cnvogelg/plipbox/hardware/nano_adapter/nano_adapter.sch

## EAGLE design hardware/nano_adapter/nano_adapter.sch (2013-05-31)

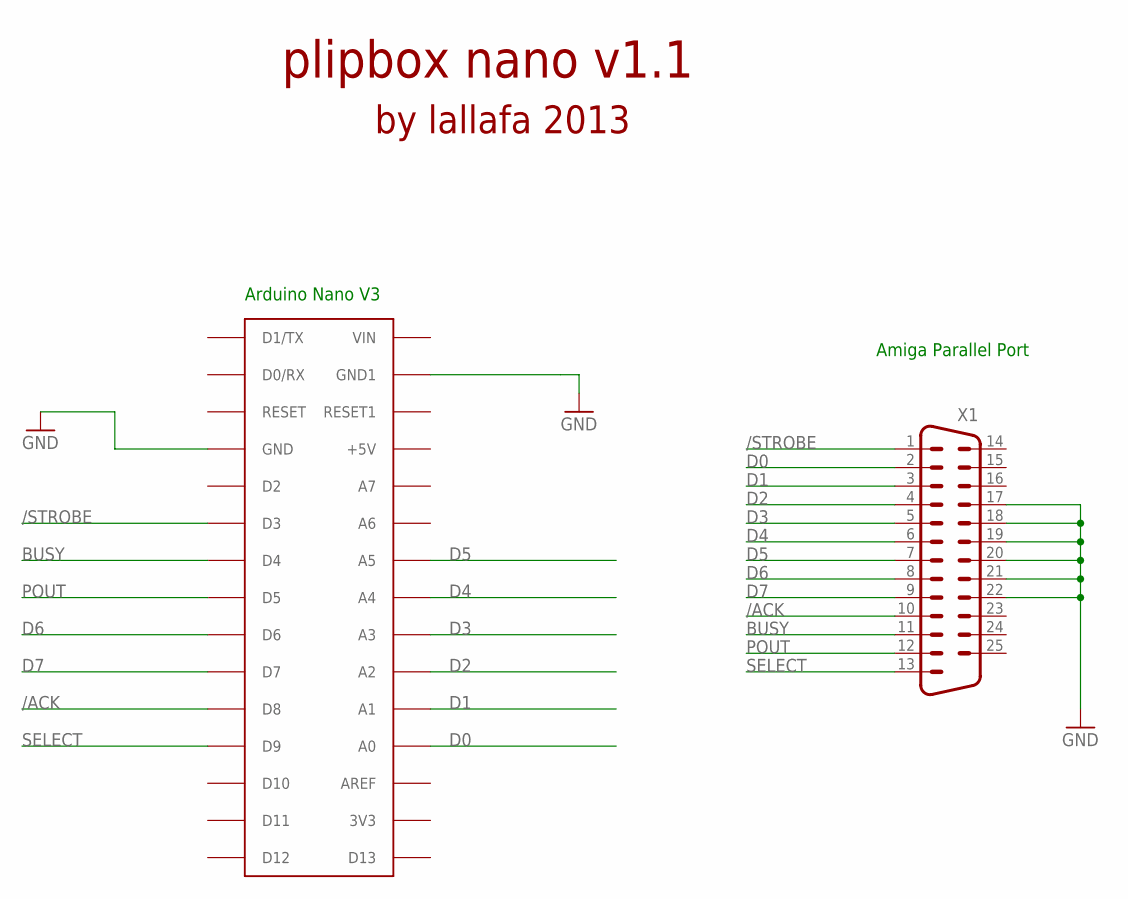
[picture p3: schematic nano_adapter.sch]

Parts:
U$1: ARDUINONANO; PDIP-32
X1: M25HP

Connections:
/ACK: U$1.D8, X1.10
/STROBE: U$1.D3, X1.1
BUSY: U$1.D4, X1.11
D0: U$1.A7 (A0), X1.2
D1: U$1.A6 (A1), X1.3
D2: U$1.A5 (A2), X1.4
D3: U$1.A4 (A3), X1.5
D4: U$1.A3 (A4), X1.6
D5: U$1.A2 (A5), X1.7
D6: U$1.D6, X1.8
D7: U$1.D7, X1.9
GND: U$1.GND, U$1.GND1, X1.17, X1.18, X1.19, X1.20, X1.21, X1.22
POUT: U$1.D5, X1.12
SELECT: U$1.D9, X1.13

Notes on the sheet:
Arduino Nano V3
Amiga Parallel Port
plipbox nano v1.1
by lallafa 2013
