cnvogelg/plipbox/avr/src/dump.c

/*
 * dump.c - helper functions for debugging
 *
 * Written by
 *  Christian Vogelgsang <chris@vogelgsang.org>
 *
 * This file is part of pbprotobox.
 * See README for copyright notice.
 *
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
 */

#include "dump.h"
#include "uart.h"
#include "uartutil.h"
#include "net/net.h"
#include "net/arp.h"
#include "net/eth.h"
#include "net/ip.h"
#include "net/udp.h"
#include "net/tcp.h"
#include "param.h"
#include "util.h"
#include "pb_proto.h"

void dump_eth_pkt(const u08 *eth_buf, u16 size)
{
  u08 buf[4];
  
  uart_send('[');
  dword_to_dec(size, buf, 4, 4);
  uart_send_data(buf,4);
  uart_send(',');
  uart_send_hex_word(eth_get_pkt_type(eth_buf));
  uart_send(',');
  net_dump_mac(eth_get_src_mac(eth_buf));
  uart_send('>');
  net_dump_mac(eth_get_tgt_mac(eth_buf));
  uart_send(']');
  uart_send(' ');
}

void dump_arp_pkt(const u08 *arp_buf)
{
  uart_send_pstring(PSTR("[ARP:"));

  // ARP op
  u16 op = arp_get_op(arp_buf);
  if(op == ARP_REQUEST) {
    uart_send_pstring(PSTR("REQ "));
  } else if(op == ARP_REPLY) {
    uart_send_pstring(PSTR("REPL"));
  } else {
    uart_send_hex_word(op);
  }
  uart_send(',');
  
  // src pair
  uart_send('(');
  net_dump_mac(arp_get_src_mac(arp_buf));
  uart_send(',');
  net_dump_ip(arp_get_src_ip(arp_buf));
  uart_send(')');
  uart_send('>');

  // tgt pair
  uart_send('(');
  net_dump_mac(arp_get_tgt_mac(arp_buf));
  uart_send(',');
  net_dump_ip(arp_get_tgt_ip(arp_buf));
  uart_send(')');
  
  uart_send(']');
  uart_send(' ');
}

void dump_ip_pkt(const u08 *ip_buf)
{
  uart_send_pstring(PSTR("[IP4:"));

  // size
  uart_send_hex_word(ip_get_total_length(ip_buf));

  // ip proto
  u08 proto = ip_get_protocol(ip_buf);
  if(proto == IP_PROTOCOL_ICMP) {
    uart_send_pstring(PSTR(",ICMP"));
  } else if(proto == IP_PROTOCOL_TCP) {
    uart_send_pstring(PSTR(",TCP "));
  } else if(proto == IP_PROTOCOL_UDP) {
    uart_send_pstring(PSTR(",UDP "));
  } else {
    uart_send(',');
    uart_send_hex_word(proto);
  }

  // src/tgt ip
  uart_send(',');
  net_dump_ip(ip_get_src_ip(ip_buf));
  uart_send('>');
  net_dump_ip(ip_get_tgt_ip(ip_buf)),

  uart_send(']');
  uart_send(' ');
}

static void dump_udp_port(u16 port)
{
  if(port == 67) {
    uart_send_pstring(PSTR("BOOTPS"));
  } else if(port == 68) {
    uart_send_pstring(PSTR("BOOTPC"));
  } else {
    uart_send(' ');
    uart_send_hex_word(port);
    uart_send(' ');
  }
}

static void dump_tcp_port(u16 port)
{
  if(port == 21) {
    uart_send_pstring(PSTR("FTPctl"));
  } else if(port == 20) {
    uart_send_pstring(PSTR("FTPdat"));
  } else {
    uart_send(' ');
    uart_send_hex_word(port);
    uart_send(' ');
  }
}

extern void dump_ip_protocol(const u08 *ip_buf)
{
  const u08 *proto_buf = ip_buf + ip_get_hdr_length(ip_buf);
  u08 proto = ip_get_protocol(ip_buf);
  if(proto == IP_PROTOCOL_UDP) {
    uart_send_pstring(PSTR("[UDP:"));
    u16 src_port = udp_get_src_port(proto_buf);
    u16 tgt_port = udp_get_tgt_port(proto_buf);
    dump_udp_port(src_port);
    uart_send('>');
    dump_udp_port(tgt_port);
    uart_send(']');
    uart_send(' ');
  }
  else if(proto == IP_PROTOCOL_TCP) {
    uart_send_pstring(PSTR("[TCP:"));
    u16 src_port = tcp_get_src_port(proto_buf);
    u16 tgt_port = tcp_get_tgt_port(proto_buf);
    dump_tcp_port(src_port);
    uart_send('>');
    dump_tcp_port(tgt_port);

    u16 flags = tcp_get_flags(proto_buf);
    uart_send_pstring(PSTR(",flags="));
    uart_send_hex_word(flags);

    uart_send_pstring(PSTR(",seq="));
    u32 seq = tcp_get_seq_num(proto_buf);
    uart_send_hex_dword(seq);
    
    if(flags & TCP_FLAGS_ACK) {
      u32 ack = tcp_get_ack_num(proto_buf);
      uart_send_pstring(PSTR(",ack="));
      uart_send_hex_dword(ack);
    }
    
    uart_send(']');
    uart_send(' ');
  }
}

extern void dump_line(const u08 *eth_buf, u16 size)
{
  dump_eth_pkt(eth_buf, size);
  
  const u08 *ip_buf = eth_buf + ETH_HDR_SIZE;
  u16 type = eth_get_pkt_type(eth_buf);
  if(type == ETH_TYPE_ARP) {
    dump_arp_pkt(ip_buf);
  } else if(type == ETH_TYPE_IPV4) {
    dump_ip_pkt(ip_buf);
    dump_ip_protocol(ip_buf);
  }
}

void dump_pb_cmd(const pb_proto_stat_t *ps)
{
  u08 buf[4];
  
  uart_send_time_stamp_spc();

  // show command
  u08 cmd = ps->cmd;
  u08 is_valid = 1;
  switch(cmd) {
    case PBPROTO_CMD_SEND:
    case PBPROTO_CMD_SEND_BURST:
      break;
    case PBPROTO_CMD_RECV:
    case PBPROTO_CMD_RECV_BURST:
      break;
    default:
      is_valid = 0;
      break;
  }

  u08 status = ps->status;

  // invalid command
  if(!is_valid) {
    uart_send_pstring(PSTR("cmd="));
    uart_send_hex_byte(cmd);
    uart_send_pstring(PSTR("?? ERR:"));
    uart_send_hex_byte(status);
    uart_send_crlf();
    return;
  }

  PGM_P str = ps->is_send ? PSTR("[TX:") : PSTR("[RX:");
  uart_send_pstring(str);
  uart_send_hex_byte(cmd);

  // result
  if(status == PBPROTO_STATUS_OK) {
    uart_send_pstring(PSTR("] ok"));
  } else {
    uart_send_pstring(PSTR("] ERR:"));
    uart_send_hex_byte(status);
  }

  // packet size
  uart_send_pstring(PSTR(" n="));
  dword_to_dec(ps->size, buf, 4, 4);
  uart_send_data(buf,4);

  // packet delta
  uart_send_pstring(PSTR(" d="));
  dword_to_dec(ps->delta, buf, 4, 4);  
  uart_send_data(buf,4);

  // speed
  uart_send_pstring(PSTR(" v="));
  uart_send_rate_kbs(ps->rate);

  // request delay
  if(!ps->is_send) {
    uart_send_pstring(PSTR("  +req="));
    uart_send_delta(ps->recv_delta);
  }
  uart_send_crlf();
}
