cnvogelg/plipbox/avr/src/pb_io.c

/*
 * pb_io.c: handle incoming plipbox packets
 *
 * Written by
 *  Christian Vogelgsang <chris@vogelgsang.org>
 *
 * This file is part of plipbox.
 * See README for copyright notice.
 *
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
 */

#include "global.h"
   
#include "net/net.h"
#include "net/eth.h"
#include "net/ip.h"
#include "net/arp.h"

#include "pkt_buf.h"
#include "pktio.h"
#include "pb_proto.h"
#include "uart.h"
#include "uartutil.h"
#include "param.h"
#include "dump.h"
#include "timer.h"
#include "stats.h"
#include "eth_state.h"
#include "util.h"
#include "pb_io.h"

static u16 offset;
static u16 size;
static u08 send_magic;

// SANA driver parameters sent in magic packet
u08 sana_online;
u08 sana_mac[6];
u08 sana_version[2];

// ----- send callbacks -----

static void rx_begin(u16 *pkt_size)
{
  // start writing packet with eth header
  offset = 0;
  pktio_tx_begin(*pkt_size);
  size = *pkt_size;
}

static void rx_data(u08 *data)
{
  // clone packet to our packet buffer
  if(offset < PKT_BUF_SIZE) {
    rx_pkt_buf[offset] = *data;
  }
  
  if(offset < size) {
    // always copy to TX buffer of pktio
    pktio_tx_byte(*data);
  }

  offset ++;
}

static void rx_end(u16 pkt_size)
{
  // end range in pktio buffer
  pktio_tx_end();
  rx_pkt_size = pkt_size;
}

// ----- recv callbacks -----

static void tx_begin(u16 *pkt_size)
{
  // report size of packet
  *pkt_size = tx_pkt_size;
  offset = 0;
  size = tx_pkt_size;

  if(!send_magic) {
    pktio_rx_data_begin();
  }
}

static void tx_data(u08 *data)
{
  // clone packet to our packet buffer
  if(offset < PKT_BUF_SIZE) {
    *data = tx_pkt_buf[offset];
  } else if(offset < size) {
    *data = pktio_rx_byte();    
  } else {
    *data = 0;
  }
  offset ++;
}

static void tx_end(u16 pkt_size)
{
  // reset size of packet
  tx_pkt_size = 0;

  if(send_magic) {
    send_magic = 0;
  } else {
    pktio_rx_data_end();
    pktio_rx_end();
  }
}

// ----- function table -----

static pb_proto_funcs_t funcs = {
  .send_begin = rx_begin,
  .send_data = rx_data,
  .send_end = rx_end,
  
  .recv_begin = tx_begin,
  .recv_data = tx_data,
  .recv_end = tx_end
};

// ----- functions -----

void pb_io_init(void)
{
  pb_proto_init(&funcs);
}

static void uart_send_prefix_pbp(void)
{
  uart_send_time_stamp_spc();
  uart_send_pstring(PSTR("pbp(rx): "));
}

static void uart_send_prefix_eth(void)
{
  uart_send_time_stamp_spc();
  uart_send_pstring(PSTR("eth(TX): "));
}

//#define DEBUG

static u08 filter_arp_pkt(void)
{
  u08 *arp_buf = rx_pkt_buf + ETH_HDR_SIZE;
  u16 arp_size = rx_pkt_size;
  
  // make sure its an IPv4 ARP packet
  if(!arp_is_ipv4(arp_buf, arp_size)) {
    uart_send_prefix_pbp();
    uart_send_pstring(PSTR("ARP: type?"));
    uart_send_crlf();
    return 0;
  }

  // ARP request should now be something like this:
  // src_mac = Amiga MAC
  // src_ip = Amiga IP
  const u08 *pkt_src_mac = eth_get_src_mac(rx_pkt_buf);
  const u08 *arp_src_mac = arp_get_src_mac(arp_buf);
  
  // pkt src and arp src must be the same
  if(!net_compare_mac(pkt_src_mac, arp_src_mac) && !net_compare_zero_mac(pkt_src_mac)) {
    uart_send_prefix_pbp();
    uart_send_pstring(PSTR("ARP: pkt!=src mac!"));
    uart_send_crlf();
    return 0;
  }
  return 1;
}

static void send(void)
{
  // dump eth packet
  if(param.dump_dirs & DUMP_DIR_ETH_TX) {
    uart_send_prefix_eth();
    dump_line(rx_pkt_buf, rx_pkt_size);
    uart_send_crlf();
  }

  // finally send ethernet packet
  pktio_tx_send(rx_pkt_size);
}

static void handle_magic_online(void)
{
  net_copy_mac(eth_get_src_mac(rx_pkt_buf), sana_mac);
  const u08 *ver = eth_get_tgt_mac(rx_pkt_buf);
  sana_version[0] = ver[0];
  sana_version[1] = ver[1];
  
  // always show online state
  uart_send_prefix_pbp();
  uart_send_pstring(PSTR("online: mac="));
  net_dump_mac(sana_mac);
  uart_send_pstring(PSTR(" ver="));
  uart_send_hex_byte(sana_version[0]);
  uart_send('.');
  uart_send_hex_byte(sana_version[1]);
  uart_send_crlf();
  
  /* neet to reconfigure eth? */
  if(!net_compare_mac(sana_mac, param.mac_addr)) {
    net_copy_mac(sana_mac, param.mac_addr);
    param_save(); /* save changed mac to eeprom */
    eth_state_configure(); /* configure eth to set new mac */
  }

  /* does versions match? */
  if((sana_version[0] == VERSION_MAJ) && (sana_version[1] == VERSION_MIN)) {  
    sana_online = 1;
  } else {
    uart_send_pstring(PSTR("VERSION MISMATCH! please update firmware."));
    uart_send_crlf();
    sana_online = 0;
  }
}

static void handle_magic_offline(void)
{
  uart_send_prefix_pbp();
  uart_send_pstring(PSTR("offline"));
  uart_send_crlf();
  
  sana_online = 0;
}

#define MAGIC_ONLINE 0xffff
#define MAGIC_OFFLINE 0xfffe

// packet arrived from Amiga. now sent via Ethernet
static void handle_pb_send(u08 eth_online)
{
  u08 dump_it = param.dump_dirs & DUMP_DIR_PLIP_RX;  
  
  // got a valid packet from plip -> check type
  u16 type = eth_get_pkt_type(rx_pkt_buf);

  // dump packet?
  if(dump_it) {
    uart_send_prefix_pbp();
    dump_line(rx_pkt_buf, rx_pkt_size);
    uart_send_crlf();
  }

  // flag if packet will be sent via ethernet
  u08 send_it = 0;
  
  // ----- magic packets from SANA driver? -----
  // magic online packet?
  if(type == MAGIC_ONLINE) {
    handle_magic_online();
  }
  // magic offline packet?
  else if(type == MAGIC_OFFLINE) {
    handle_magic_offline();
  }
  else {
    // ----- packet filtering? -----
    if(param.filter_plip) {
      if(type == ETH_TYPE_IPV4) {
        send_it = 1;
      }
      // handle ARP packet
      else if(type == ETH_TYPE_ARP) {
        send_it = filter_arp_pkt();
      }
      // unknown packet type
      else {
        uart_send_prefix_pbp();
        uart_send_pstring(PSTR("type? "));
        uart_send_hex_word(type);
        uart_send_crlf();
        send_it = 0;
      }
    } else {
      send_it = 1;
    }
  }
  
  // send to ethernet
  if(send_it) {
    if(eth_online) {
      stats.tx_cnt ++;
      stats.tx_bytes += rx_pkt_size;    
      send();
    } else {
      // no ethernet online -> we have to drop packet
      uart_send_prefix_eth();
      uart_send_pstring(PSTR("Offline -> DROP!"));
      uart_send_crlf();
      stats.tx_drop ++;
      pktio_tx_reject();
    }      
  } else {
    stats.tx_filter ++;
    pktio_tx_reject();
  }    
}

void pb_io_send_magic(u16 type, u08 extra_size)
{
  // set tx packet size so no ethernet frames are written in packet buffer
  tx_pkt_size = 14 + extra_size;
  send_magic = 1;

  // fill ethernet header
  u08 *ptr = tx_pkt_buf;
  net_copy_bcast_mac(ptr);
  ptr += 6;
  net_copy_mac(param.mac_addr, ptr);
  ptr += 6;
  net_put_word(ptr, type);

  // now request receive from Amiga
  pb_proto_request_recv();

  // report
  uart_send_prefix_pbp();
  uart_send_pstring(PSTR("send magic "));
  uart_send_hex_word(type);
  uart_send_crlf();
}

extern u32 req_time;

u08 pb_io_worker(u08 plip_state, u08 eth_online)
{
  // call protocol handler (low level transmit)
  u08 cmd;
  u16 size;
  u32 start = time_stamp;
  u08 status = pb_proto_handle(&cmd, &size);
  u32 end = time_stamp;
  
  // nothing done... return
  if(status == PBPROTO_STATUS_IDLE) {
    return PB_IO_IDLE; // was passive
  }
  else if(status == PBPROTO_STATUS_OK) {
    u32 delta = end - start;

    // dump ok command if requested
    if(param.dump_plip) {
      dump_pb_cmd(cmd, status, size, delta, start - req_time);
    }
    
    // do we have a packet received?
    if((cmd == PBPROTO_CMD_SEND) || (cmd == PBPROTO_CMD_SEND_BURST)) {
      handle_pb_send(eth_online);
    }

    // update rate
    u16 rate = calc_rate_kbs(size, delta);
    if(cmd == PBPROTO_CMD_SEND) {
      if(rate > stats.tx_max_rate) {
        stats.tx_max_rate = rate;
      }
    } else {
      if(rate > stats.rx_max_rate) {
        stats.rx_max_rate = rate;
      }
    }
    return PB_IO_OK;
  }
  else {
    u32 delta = end - start;
    u32 latency = start - req_time;
    
    // dump error
    dump_pb_cmd(cmd, status, size, delta, latency);

    return PB_IO_ERROR;
  }
}
