cnvogelg/plipbox/src/eth_tx.c

/*
 * eth_tx.c: handle eth packet sends
 *
 * Written by
 *  Christian Vogelgsang <chris@vogelgsang.org>
 *
 * This file is part of plip2slip.
 * See README for copyright notice.
 *
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
 */

#include "global.h"
   
#include "net.h"
#include "eth.h"
#include "ip.h"
#include "arp.h"
#include "icmp.h"
#include "pkt_buf.h"
#include "enc28j60.h"

#include "plip.h"

#include "uart.h"
#include "uartutil.h"
   
#define DEBUG_ETH_TX   

u08 eth_tx_send_ping_request(const u08 *ip)
{
#ifdef DEBUG_ETH_TX
  uart_send_string("send ping: ");
  net_dump_ip(ip);
#endif

  const u08 *mac = arp_find_mac(pkt_buf, ip);
  if(mac == 0) {
#ifdef DEBUG_ETH_TX
    uart_send_string("no mac!");
    uart_send_crlf();
#endif
    return 0;
  }
  
#ifdef DEBUG_ETH_TX
  uart_send_string(" -> ");
  net_dump_mac(mac);
  uart_send_crlf();
#endif
  
  eth_make_to_tgt(pkt_buf, ETH_TYPE_IPV4, mac);
  u08 *ip_pkt = pkt_buf + ETH_HDR_SIZE;
  u16 size = icmp_make_ping_request(ip_pkt, ip, 0, 0);
  enc28j60_packet_tx(pkt_buf, size + ETH_HDR_SIZE);
  
  return 1;
}

static void handle_my_packet(u08 *ip_buf, u16 size)
{
  // TODO
}

static u08 offset;

static u08 begin_rx(plip_packet_t *pkt)
{
  // start writing packet after (potential) ETH header
  offset = ETH_HDR_SIZE;
  
  // start writing after ETH header
  enc28j60_packet_tx_begin_range(ETH_HDR_SIZE);
  
  return PLIP_STATUS_OK;
}

static u08 transfer_rx(u08 *data)
{
  // clone packet to our packet buffer
  if(offset < PKT_BUF_SIZE) {
    pkt_buf[offset] = *data;
    offset ++;
  }
  
  // always copy to TX buffer of enc28j60
  enc28j60_packet_tx_byte(*data);
  
  return PLIP_STATUS_OK;
}

static u08 end_rx(plip_packet_t *pkt)
{
  // end range in enc28j60 buffer
  enc28j60_packet_tx_end_range();

  return PLIP_STATUS_OK;
}

void eth_tx_init(void)
{
  plip_recv_init(begin_rx, transfer_rx, end_rx);
}

void eth_tx_worker(void)
{
  // do we have a PLIP packet waiting?
  if(plip_can_recv() == PLIP_STATUS_OK) {
    
    // prepare eth chip to get its tx buffer filled
    enc28j60_packet_tx_prepare();
    
    // receive PLIP packet and store it in eth chip tx buffer
    // also keep a copy in our local pkt_buf (up to max size)
    u08 status = plip_recv(&pkt);
    
    // if PLIP rx was ok then have a look at the packet
    if(status != PLIP_STATUS_OK) {
      uart_send_string("plip_rx:");
      uart_send_hex_byte_crlf(status);
    } else {
      // fetch tgt ip of incoming packet
      u08 *ip_buf = pkt_buf + ETH_HDR_SIZE;
      const u08 *tgt_ip = ip_get_tgt_ip(ip_buf);
      u08 ltgt_ip[4];
      net_copy_ip(tgt_ip, ltgt_ip);
      const u08 *src_ip = ip_get_src_ip(ip_buf);
  
      // make sure all packets are coming from amiga
      if(!net_compare_ip(src_ip, net_get_p2p_amiga())) {
        uart_send_string("plip_rx: not amiga!");
        uart_send_crlf();
        return;
      }
  
      // if its a packet for me (p2p or eth address) then handle it now
      if(net_compare_ip(ltgt_ip, net_get_p2p_me()) ||
         net_compare_ip(ltgt_ip, net_get_ip())) {
        uart_send_string("plip_rx: ME!");
        uart_send_crlf();
        handle_my_packet(ip_buf, pkt.size);
      } 
      // pass this packet on to ethernet
      else {
#ifdef DEBUG
        uart_send_string("plip_rx:");
        net_dump_ip(ltgt_ip);
        uart_send_string(" size=");
        uart_send_hex_word_spc(pkt.size);
#endif
        
        // find a mac address for the target 
        const u08 *mac = arp_find_mac(pkt_buf, ltgt_ip);
        if(mac == 0) {
          uart_send_string("??");
          uart_send_crlf();
        }
        // found mac -> we can send packet
        else {
#ifdef DEBUG
          uart_send_string(" -> mac ");
          net_dump_mac(mac);
          uart_send_crlf();
#endif
        
          // ----- NAT -----
          // adjust source ip to our eth IP
          ip_adjust_checksum(ip_buf, IP_CHECKSUM_OFF, net_get_p2p_amiga(), net_get_ip());
          
          // get protocol
          u08 protocol = ip_get_protocol(ip_buf);
          u16 copy_size = ETH_HDR_SIZE + IP_MIN_HDR_SIZE;
          if(protocol == IP_PROTOCOL_TCP) {
            // adjust TCP checksum
            u16 off = ip_get_hdr_length(ip_buf) + TCP_CHECKSUM_OFF;
            ip_adjust_checksum(ip_buf, off, net_get_p2p_amiga(), net_get_ip());
            copy_size += TCP_CHECKSUM_OFF + 2;
          } else if(protocol == IP_PROTOCOL_UDP) {
            // adjust UDP checksum
            u16 off = ip_get_hdr_length(ip_buf) + UDP_CHECKSUM_OFF;
            ip_adjust_checksum(ip_buf, off, net_get_p2p_amiga(), net_get_ip());
            copy_size += UDP_CHECKSUM_OFF + 2;
          }

          // change src ip to my eth ip
          ip_set_src_ip(ip_buf, net_get_ip());
          
#ifdef DEBUG
          // make sure our checksum was corrected correctly
          u16 chk = ip_hdr_calc_checksum(ip_buf);
          if(chk != 0xffff) {
            uart_send_string("eth_tx:CHECK?");
            uart_send_hex_word_crlf(chk);
          }
#endif
        
          // now build ethernet header
          eth_make_to_tgt(pkt_buf, ETH_TYPE_IPV4, mac);
        
          // copy (created) eth header and (modified) ip header back to packet buffer
          enc28j60_packet_tx_begin_range(0);
          enc28j60_packet_tx_blk(pkt_buf, copy_size);
          enc28j60_packet_tx_end_range();
  
          // finally send packet
          u16 pkt_size = pkt.size + ETH_HDR_SIZE;
          enc28j60_packet_tx_send(pkt_size);
        }
      }
    }
  }
}
