cnvogelg/plipbox/avr/src/param.c

/*
 * param.c - handle device parameters
 *
 * Written by
 *  Christian Vogelgsang <chris@vogelgsang.org>
 *
 * This file is part of plipbox.
 * See README for copyright notice.
 *
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
 */

#include "param.h"
#include "uartutil.h"
#include "uart.h"
#include "net/net.h"

#include <avr/eeprom.h>
#include <util/crc16.h>
#include <avr/pgmspace.h>
#include <string.h>

// current memory RAM param
param_t param;

// eeprom param
param_t eeprom_param EEMEM;
uint16_t eeprom_crc16 EEMEM;

// default 
static const param_t PROGMEM default_param = {
  .mac_addr = { 0x1a,0x11,0xaf,0xa0,0x47,0x11},

  .flow_ctl = 0,
  .full_duplex = 0,
  
  .test_plen = 1514,
  .test_ptype = 0xfffd,
  .test_ip = { 192,168,2,222 },
  .test_port = 6800,
  .test_mode = 0
};

static void dump_byte(PGM_P str, const u08 val)
{
  uart_send_pstring(str);
  uart_send_hex_byte(val);
  uart_send_crlf();  
}

static void dump_word(PGM_P str, const u16 val)
{
  uart_send_pstring(str);
  uart_send_hex_word(val);
  uart_send_crlf();    
}

// dump all params
void param_dump(void)
{
  // mac address
  uart_send_pstring(PSTR("m: mac address   "));
  net_dump_mac(param.mac_addr);
  uart_send_crlf();

  // options
  uart_send_crlf();
  dump_byte(PSTR("fd: full duplex  "), param.full_duplex);
  dump_byte(PSTR("fc: flow control "), param.flow_ctl);
  
  // test
  uart_send_crlf();
  dump_word(PSTR("tl: packet len   "), param.test_plen);
  dump_word(PSTR("tt: packet type  "), param.test_ptype);
  uart_send_pstring(PSTR("ti: ip address   "));
  net_dump_ip(param.test_ip);
  uart_send_crlf();
  dump_word(PSTR("tp: udp port     "), param.test_port);
  dump_byte(PSTR("tm: test mode    "), param.test_mode);
}

// build check sum for parameter block
static uint16_t calc_crc16(param_t *p)
{
  uint16_t crc16 = 0xffff;
  u08 *data = (u08 *)p;
  for(u16 i=0;i<sizeof(param_t);i++) {
    crc16 = _crc16_update(crc16,*data);
    data++;
  }
  return crc16;
}

u08 param_save(void)
{
  // check that eeprom is writable
  if(!eeprom_is_ready())
    return PARAM_EEPROM_NOT_READY;

  // write current param to eeprom
  eeprom_write_block(&param,&eeprom_param,sizeof(param_t));

  // calc current parameter crc
  uint16_t crc16 = calc_crc16(&param);
  eeprom_write_word(&eeprom_crc16,crc16);

  return PARAM_OK;
}

u08 param_load(void)
{
  // check that eeprom is readable
  if(!eeprom_is_ready())
    return PARAM_EEPROM_NOT_READY;
  
  // read param
  eeprom_read_block(&param,&eeprom_param,sizeof(param_t));
  
  // read crc16
  uint16_t crc16 = eeprom_read_word(&eeprom_crc16);
  uint16_t my_crc16 = calc_crc16(&param);
  if(crc16 != my_crc16) {
    param_reset();
    return PARAM_EEPROM_CRC_MISMATCH;
  }
  
  return PARAM_OK;
}

void param_reset(void)
{
  // restore default param
  u08 *out = (u08 *)&param;
  const u08 *in = (const u08 *)&default_param;
  for(u08 i=0;i<sizeof(param_t);i++) {
    *(out++) = pgm_read_byte_near(in++);
  }
}

void param_init(void)
{
  if(param_load()!=PARAM_OK)
    param_reset();
}
