cnvogelg/plipbox/avr/src/pb_proto.h

/*
 * pb_proto.h - avr implementation of the plipbox protocol
 *
 * Written by
 *  Christian Vogelgsang <chris@vogelgsang.org>
 *
 * This file is part of plipbox.
 * See README for copyright notice.
 *
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
 */

#ifndef PBPROTO_H
#define PBPROTO_H

#include "global.h"

// status return
#define PBPROTO_STATUS_IDLE              0
#define PBPROTO_STATUS_OK                1
#define PBPROTO_STATUS_TIMEOUT           2
#define PBPROTO_STATUS_LOST_SELECT       3
#define PBPROTO_STATUS_INVALID_CMD       4
#define PBPROTO_STATUS_PACKET_TOO_LARGE  5
#define PBPROTO_STATUS_ERROR             6

// protocol stages for error reprots
#define PBPROTO_STAGE_END_SELECT         0x10
#define PBPROTO_STAGE_SIZE_HI            0x20
#define PBPROTO_STAGE_SIZE_LO            0x30
#define PBPROTO_STAGE_DATA               0x40
#define PBPROTO_STAGE_LAST_DATA          0x50
#define PBPROTO_STAGE_BURST_LO           0x60
#define PBPROTO_STAGE_BURST_HI           0x70
#define PBPROTO_STAGE_INPUT              0x80

// commands
#define PBPROTO_CMD_SEND       0x11   // amiga wants to send a packet
#define PBPROTO_CMD_RECV       0x22   // amiga wants to receive a packet
#define PBPROTO_CMD_SEND_BURST 0x33
#define PBPROTO_CMD_RECV_BURST 0x44

// line status
#define PBPROTO_LINE_OFF       0x0
#define PBPROTO_LINE_DISABLED  0x7
#define PBPROTO_LINE_OK        0x1

// callbacks
typedef u08 (*pb_proto_fill_func)(u08 *buf,u16 max_size,u16 *size);
typedef u08 (*pb_proto_proc_func)(const u08 *buf, u16 size);

typedef struct {
  u08 cmd;		// received pb proto command
  u08 status;   // status after processing the command
  u08 is_send;    // was a transmit command (amiga send?)
  u08 stats_id; // what id to use for stats recording
  u16 size;     // packet size 
  u16 delta;    // hw timing for transmit
  u16 rate;     // delta converted to transfer rate
  u16 recv_delta; // delta after recv was requested 
  u32 ts;       // time stamp of transfer
} pb_proto_stat_t;

extern pb_proto_stat_t pb_proto_stat; // filled by pb_proto_handle()

// ----- Parameter -----

extern u16 pb_proto_rx_timeout; // timeout for next byte in 100us

// ----- API -----

extern void pb_proto_init(pb_proto_fill_func fill_func, pb_proto_proc_func proc_func, u08 *buf, u16 buf_size);
extern u08  pb_proto_get_line_status(void);
extern u08  pb_proto_handle(void); // side effect: fill pb_proto_stat!
extern void pb_proto_request_recv(void);

#endif
