cnvogelg/plipbox/avr/src/pio.c

/*
 * pio.c - generic interface for packet I/O
 *
 * Written by
 *  Christian Vogelgsang <chris@vogelgsang.org>
 *
 * This file is part of plipbox.
 * See README for copyright notice.
 *
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
 */

#include "pio.h"
#include "pio_dev.h"
#include "uartutil.h"
#include "net/net.h"

#ifdef DEV_ENC28J60
#include "enc28j60.h"
#endif

// the table of available devices
static const pio_dev_ptr_t PROGMEM devices[] = {
#ifdef DEV_ENC28J60
  &pio_dev_enc28j60,
#endif
};
#define NUM_DEVICES  (sizeof(devices) / sizeof(pio_dev_ptr_t))

// index of active device
static u08 dev_id;
static pio_dev_ptr_t cur_dev;

u08 pio_set_device(u08 id)
{
  if(id < NUM_DEVICES) {
    dev_id = id;
    return 1;
  }
  // invalid device selected
  return 0;
}

u08 pio_init(const u08 mac[6],u08 flags)
{
  // get current device
  cur_dev = (pio_dev_ptr_t)pgm_read_word(devices + dev_id);

  // show hello
  uart_send_time_stamp_spc();
  uart_send_pstring(PSTR("pio: init: "));
  PGM_P name = pio_dev_name(cur_dev);
  uart_send_pstring(name);

  // call init
  u08 result = pio_dev_init(cur_dev, mac, flags);
  if(result == PIO_OK) {
    uart_send_pstring(PSTR(": ok! mac="));
    net_dump_mac(mac);
    uart_send_pstring(PSTR(" flags="));
    uart_send_hex_byte(flags);
    // show revision
    u08 rev;
    result = pio_dev_status(cur_dev, PIO_STATUS_VERSION, &rev);
    if(result == PIO_OK) {
      uart_send_pstring(PSTR(" rev="));
      uart_send_hex_byte(rev);
    }
  } else {
    uart_send_pstring(PSTR("ERROR:"));
    uart_send_hex_byte(result);
  }
  uart_send_crlf();
  return result;
}

void pio_exit(void)
{
  uart_send_time_stamp_spc();
  uart_send_pstring(PSTR("pio: exit\r\n"));
  pio_dev_exit(cur_dev);
}

u08 pio_send(const u08 *buf, u16 size)
{
  return pio_dev_send(cur_dev, buf, size);
}

u08 pio_recv(u08 *buf, u16 max_size, u16 *got_size)
{
  return pio_dev_recv(cur_dev, buf, max_size, got_size);
}

u08 pio_has_recv(void)
{
  return pio_dev_has_recv(cur_dev);
}

u08 pio_status(u08 status_id, u08 *value)
{
  return pio_dev_status(cur_dev, status_id, value);
}

u08 pio_control(u08 control_id, u08 value)
{
  return pio_dev_control(cur_dev, control_id, value);
}
