cnvogelg/plipbox/avr/src/base/util.c

/*
 * util.c - utilities
 *
 * Written by
 *  Christian Vogelgsang <chris@vogelgsang.org>
 *
 * This file is part of plipbox.
 * See README for copyright notice.
 *
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
 */

#include "util.h"

// convert to hex

u08 nybble_to_hex(u08 in)
{
  if(in<10)
    return '0' + in;
  else
    return 'A' + in - 10;
}

void byte_to_hex(u08 in,u08 *out)
{
  out[0] = nybble_to_hex(in >> 4);
  out[1] = nybble_to_hex(in & 0xf);
}

void word_to_hex(u16 in,u08 *out)
{
  byte_to_hex((u08)(in>>8),out);
  byte_to_hex((u08)(in&0xff),out+2);
}

void dword_to_hex(u32 addr,u08 *out)
{
  word_to_hex((u16)(addr>>16),out);
  word_to_hex((u16)(addr&0xffff),out+4);
}

void byte_to_dec(u08 value, u08 *out)
{
  u08 h = value / 100;
  u08 t = value % 100;
  u08 o = t % 10;
  t = t / 10;
  out[0] = '0' + h;
  out[1] = '0' + t;
  out[2] = '0' + o;
}

void dword_to_dec(u32 value, u08 *out, u08 num_digits, u08 point_pos)
{
  // start backwards
  u08 *pos = out + num_digits - 1;
  if(point_pos < num_digits) {
    pos++;
  }
  for(u08 i=0;i<num_digits;i++) {
    if(i == point_pos) {
      *pos = '.';
      pos--;
    }
    u08 dec = value % 10;
    *pos = '0' + dec;
    pos--;
    value /= 10;
  }
}

// parse

u08 parse_nybble(u08 c,u08 *value)
{
  if((c>='a')&&(c<='f')) {
    *value = c + 10 - 'a';
    return 1;
  } 
  else if((c>='A')&&(c<='F')) {
    *value = c + 10 - 'A';
    return 1;
  } 
  else if((c>='0')&&(c<='9')) {
    *value = c - '0';
    return 1;
  } 
  else
    return 0;
}

u08 parse_byte(const u08 *str,u08 *value)
{
  u08 val;
  if(!parse_nybble(str[0],&val))
    return 0;
  val <<= 4;
  if(!parse_nybble(str[1],value))
    return 0;
  *value |= val;
  return 1;
}

u08 parse_word(const u08 *str,u16 *value)
{
  u08 val;
  if(!parse_byte(&str[0],&val))
    return 0;
  u08 val2;
  if(!parse_byte(&str[2],&val2))
    return 0;
  *value = (u16)val << 8 | val2;
  return 1;
}

u08 parse_dword(const u08 *str,u32 *value)
{
  u08 val;
  if(!parse_byte(&str[0],&val))
    return 0;
  u08 val2;
  if(!parse_byte(&str[2],&val2))
    return 0;
  u08 val3;
  if(!parse_byte(&str[4],&val3))
    return 0;
  u08 val4;
  if(!parse_byte(&str[6],&val4))
    return 0;
  *value = (u32)val << 24 | (u32)val2 << 16 | (u32)val3 << 8 | val4;
  return 1;
}

u08 parse_byte_dec(const u08 *buf, u08 *out)
{
  u08 value = 0;
  u08 digits = 0;
  while(digits < 3) {
    u08 c = buf[digits];
    if((c<'0')||(c>'9')) {
      break;
    }
    c -= '0';
    value *= 10;
    value += c;
    digits++;
  }
  if(digits > 0) {
    *out = value;
  }
  return digits;
}
